ionizing-radar/mwr/shapes/10mm hole - LH drive wheel arm v2.stl

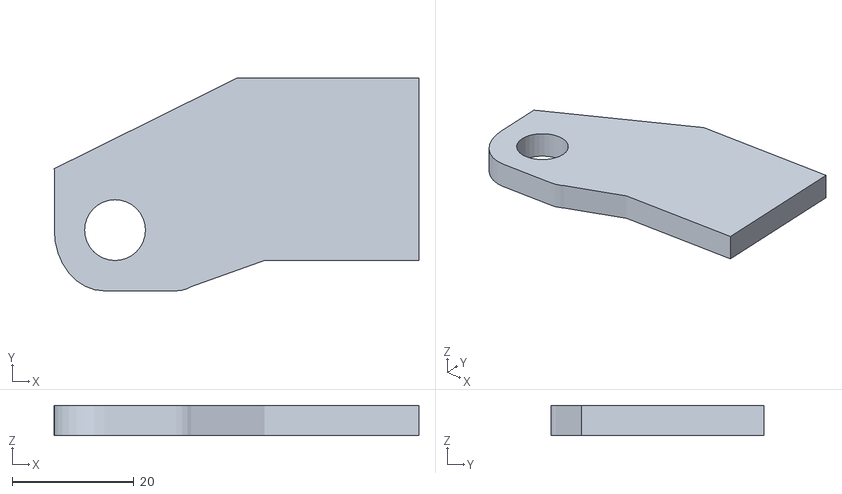
[picture p16: CAD file, 2020-08-06]
shapes/10mm hole - LH drive wheel arm v2.stl
60.0 x 35.0 x 5.00
