ionizing-radar/mwr/shapes/ULN2003 mount.stl

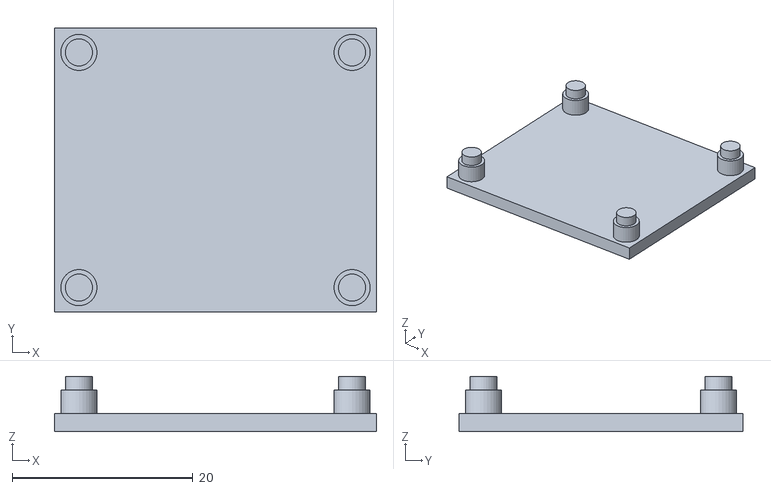
[picture p17: CAD file, 2020-08-05]
shapes/ULN2003 mount.stl
35.6 x 31.4 x 6.11
